doodeca/crownstone-2wire-dimmerswitch/documents/architecture/dfd0.png

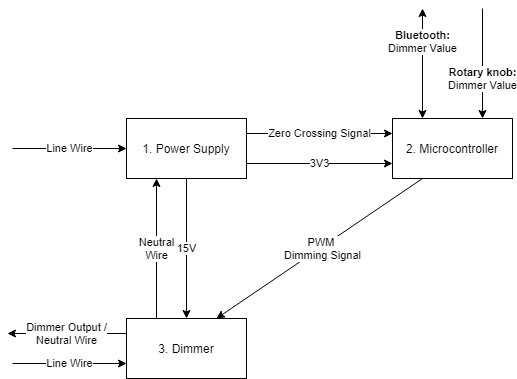
documents/architecture/dfd0.png
