doodeca/crownstone-2wire-dimmerswitch/documents/architecture/dfd1.png

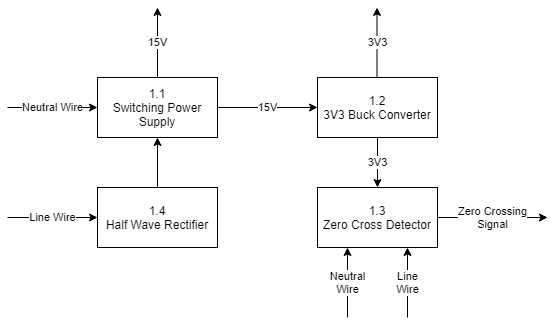
documents/architecture/dfd1.png
