doodeca/crownstone-2wire-dimmerswitch/documents/architecture/dfd3.png

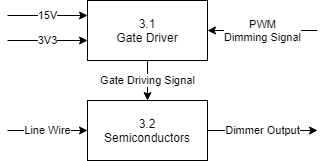
documents/architecture/dfd3.png
