doodeca/crownstone-2wire-dimmerswitch/documents/design/simplified_schematic_lnk302.PNG

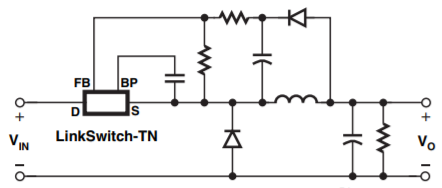
documents/design/simplified_schematic_lnk302.PNG
