doodeca/crownstone-2wire-dimmerswitch/hardware/simulations/Pspice/LINKSWITCH-TN.png

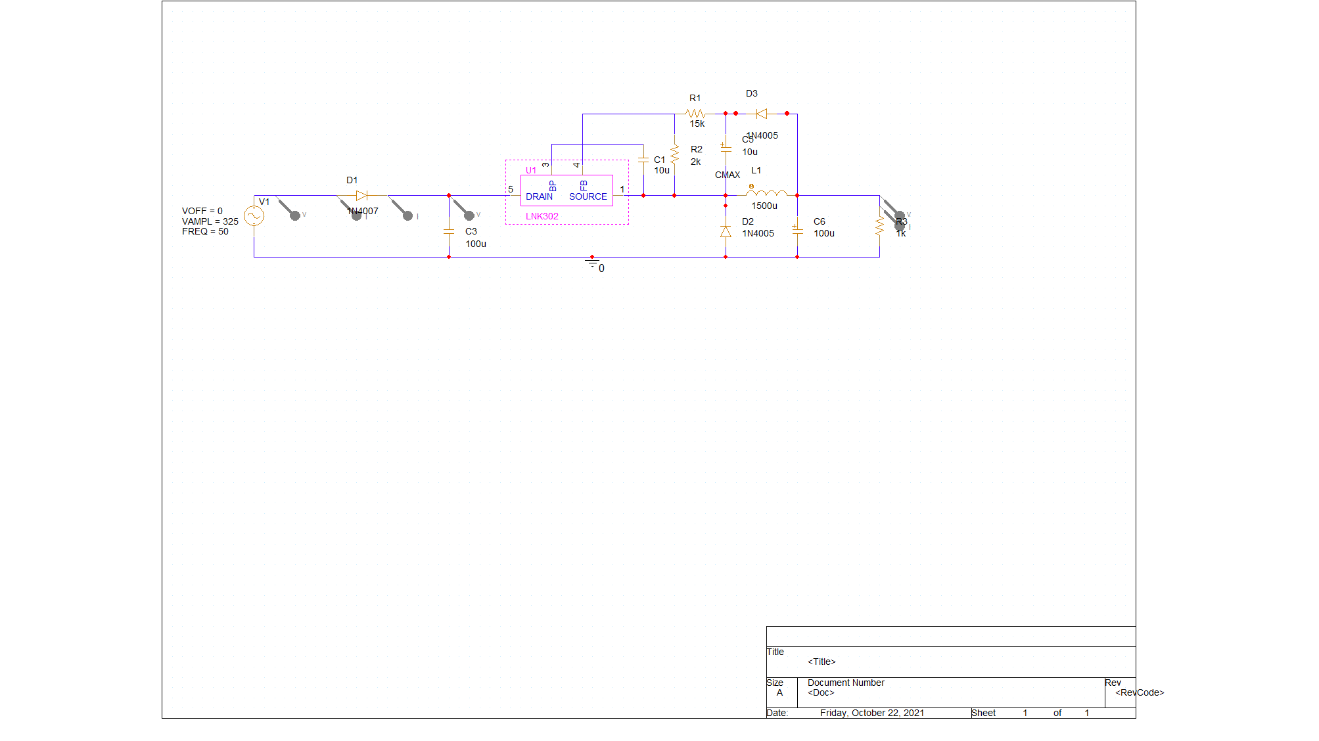
hardware/simulations/Pspice/LINKSWITCH-TN.png
