doodeca/crownstone-2wire-dimmerswitch/hardware/simulations/LTspice/zcd-opamp.asc

B1: bv; V=white(2e5*time)*100
R1: res; 10Meg
R2: res; 100k
R3: res; 10Meg
R4: res; 10Meg
R5: res; 100k
R6: res; 10Meg
U1: UniversalOpamp2; Avol=1Meg GBW=1Meg Slew=600Meg; Ilimit=20m Rail=0 Vos=0.001 Phimargin=45
U2: UniversalOpamp2; Avol=100k GBW=1Meg Slew=600k; Ilimit=20m Rail=0 Vos=0.001 Phimargin=45
V1: voltage; SINE(0 325 50)
V2: voltage; 3.3
V3: voltage; SINE(0 325 50)
Named nets: 3v3, 0, V_in_noise, V_in, V_out_noise, V_out
.tran 0.1
