doodeca/crownstone-2wire-dimmerswitch/hardware/simulations/LTspice/15-3v3-buck.asc

B1: bv; V=15+(white(2e5*time))
C1: cap; 1µ
C2: cap; 10p
C3: cap; 22µ
C4: cap; 0.1µ
C5: cap; 100µ
D1: schottky; CMDSH2-3
D2: schottky; MBRS340
L1: ind; 100µ; Ipk=0.26 Rser=1.59 Rpar=0 Cpar=0 mfg="Murata" pn="LQH3NPN101MMEL"
R1: res; 620k
R2: res; 1Meg
R3: res; 200
R4: res; 0.0001
R5: res; 0.0001
U1: LT1934-1
V1: voltage; SINE(15 0.15 64k)
V2: voltage; 15
Named nets: 0, V_out, V_in
.tran 0.005
